mattico/high-gain-diff-probe/Sim/Comparator.asc

C1: cap; 0.1µ
C3: cap; 0.1µ
C4: cap; 10n
C5: cap; 0.1µ
D1: LED; NSCW100
R1: res; 7.15k
R2: res; 100k
R3: res; 7.15k
R4: res; 7.15k
R5: res; 7.15k
R6: res; 7.15k
R7: res; 10Meg
R8: res; 7.15k
R9: res; 100k
U1: LT1011
U2: LT1011
U3: LT1011
V1: voltage; 15
V2: voltage; 15
V3: voltage; PULSE(0 20 1m 10u 10u 0.1m); AC 1; Rser=50 Cpar=0.04p
Named nets: 0, +V, -V, IN, OUT, RC
.tran 0 50m 0
