mattico/high-gain-diff-probe/Sim/PowerInput_Boost_LT3580.asc

C1: cap; 10µ; V=25 Irms=0 Rser=0 Lser=0 mfg="Murata" pn="GRM21BZ71E106KE15" type="X7R"
C2: cap; 2.2n; Rser=10K
C3: cap; .1µ
C4: cap; 10µF
C5: cap; 1µ
C6: cap; 100p
C7: polcap; 47µ; V=25 Irms=70m Rser=0.526 Lser=18.5243n mfg="Würth Elektronik" pn="865090449007 WCAP-ASLU 8x6,5" type="Al electrolytic"
D1: schottky; 1N5818
L1: ind2; 27µ; Rser=.285
L2: ind2; 27µ; Rser=.285
R1: res; 450k
R2: res; 180k
Rload: res; 100
U1: LT3580
V1: voltage; 4.5; Rser=.5
Named nets: 0, IN, OUT
.tran 0 1m 0 10n startup
K1 L1 L2 1
