mattico/high-gain-diff-probe/Sim/PowerInput_LTM8049.asc

C3: cap; 10µ
C4: cap; 47µ; V=16 Irms=11.7 Rser=0.00333036 Lser=0 mfg="KEMET" pn="C1210C476K4PAC" type="X5R"
C5: cap; 22µ; V=25 Irms=0 Rser=0 Lser=0 mfg="Murata" pn="GRM32ER71E226KE15" type="X7R"
R1: res; 73.2k
R2: res; 165k
R3: res; 73.2k
R4: res; 178k
Rload1: res; 150
Rload2: res; 150
U1: LTM8049
V1: voltage; 4.5; Rser=0.4
Named nets: 0, IN, OUT1, OUT2
.tran 2m
