mattico/high-gain-diff-probe/Sim/PowerInput_Boost_LDO.asc

C1: cap; 1µ; V=25 Irms=0 Rser=0.001 Lser=0
C2: cap; 1µ; V=25 Irms=0 Rser=0.001 Lser=0
C3: cap; 1µ; V=35 Irms=0 Rser=0 Lser=0 mfg="Murata" pn="GCM21BR7YA105MA55" type="X7R"
C4: cap; 1µ; V=25 Irms=0 Rser=0 Lser=0 mfg="Murata" pn="GCM188R71E105MA64" type="X7R"
C5: cap; 10p; V=25 Irms=0 Rser=0 Lser=0 mfg="Murata" pn="GCM0335C1E100JA16" type="C0G"
C6: cap; 1µ; V=25 Irms=0 Rser=0.001 Lser=0 mfg="TDK" pn="C575OX7RIE106M" type="X7R"
C7: cap; 1µ; V=25 Irms=0 Rser=0.001 Lser=0 mfg="TDK" pn="C575OX7RIE106M" type="X7R"
C8: cap; 10µ; V=6.3 Irms=0 Rser=0 Lser=0 mfg="Murata" pn="GRM188R60J106ME84" type="X5R"
C9: polcap; 47µ; V=25 Irms=36m Rser=1.35945 Lser=2.49256n
C10: polcap; 47µ; V=25 Irms=36m Rser=1.35945 Lser=2.49256n
C11: cap; 1µ; V=25 Irms=0 Rser=0.00804838 Lser=269.844p mfg="Würth Elektronik" pn="885012207078 WCAP-CSGP 0805" type="X7R"
D1: schottky; MBRS130L
D2: diode; BAV199HM
D3: diode; BAV199HM
D4: diode; BAV199HM
D8: diode; BAV199HM
L1: ind; 22µ; Ipk=0.92 Rser=0.348
L2: ind; 22µ; Ipk=0.92 Rser=0.348
R1: res; 300k
R2: res; 1Meg
R3: res; 88k
R5: res; 1Meg
R6: res; 75k
R7: res; 83k
R8: res; 1Meg
RLoad1: res; 200
RLoad: res; 200
RProbe: res; 50
RTerm: res; 50k
U1: LT3088
U3: LT3463
U4: LT3015
V1: voltage; 4.5; Rser=0.6
Named nets: VOUT+, VOUT-, 0, VIN, VINT+, VINT-, FB1, FB2
.tran 0 10m 0 10n
;.ac dec 100 1 3.5Meg
