mattico/high-gain-diff-probe/Sim/DiffAmp_AD8428.asc

C1: cap; 10.4p
C2: cap; 10.4p
C3: cap; 1n
C4: cap; 1n
C11: cap; 10µ
D1: diode; BAV199HM
D2: diode; BAV199HM
D3: diode; BAV199HM
D4: diode; BAV199HM
D5: diode; BAV199HM
D6: diode; BAV199HM
R1: res; 33; tol=0.1
R2: res; 33; tol=0.1
R3: res; 50
R4: res; 225
R5: res; 33; tol=0.1
R6: res; 33; tol=0.1
R9: res; 10100
R10: res; 990k
R11: res; 10100
R13: res; 10.78k
R14: res; 11k
R15: res; 200; tol=0.1
R17: res; 225
R19: res; 1Meg
R20: res; 1Meg
R: res; 990k
U1: AD8428
U2: BUF634A
U3: OP1177
U4: AD8671
V1: voltage; 15; Rser=0
V2: voltage; 15; Rser=0
VDiff: voltage; SINE(0 .01 100k); AC 1
Named nets: -V, +V, 0, IN+, IN-, ATTEN+, ATTEN-, OUT, SE
.op
;.ac dec 100 10 10Meg
.tran 0 100u 0
;.noise V(OUT) VDiff dec 100 0.1 1Meg
Optional parallel InAmps to reduce noise. Increases output offset voltage.
Only effective when amplifier noise dominates input resistance noise.
AC Input: Reduces flatband noise by 1/2
HiZ Input: Increases noise
LoZ Input: Decreases noise by 20%
0 Ohm Input: Decreases noise by 25%
 
Sometimes they need to be deleted for the output simulation to work,
it'll output SNAN otherwise.
Offset Trim
Switchable 100kHz Low-Pass
100kHz: 8.2nF
Switchable Gain Resistor:
2000X - None
1000X - 6000 ohm
500X - 2000
100X - 316
50X - 154
10X - 30.2
