mattico/high-gain-diff-probe/Sim/DiffAmp_AD8428_Opt.asc

C1: cap; 8p
C4: cap; 14.7p
C5: cap; 14.7p
C9: cap; 1.5µ; V=100
C10: cap; 1.5µ; V=100
C11: cap; 10µ
C12: cap; 33n
C13: cap; 40p
C14: cap; 40p
D1: diode; BAV199HM
D2: diode; BAV199HM
D3: diode; BAV199HM
D4: diode; BAV199HM
D5: diode; BAV199HM
D6: diode; BAV199HM
R1: res; 950k
R2: res; 950k
R3: res; 50
R4: res; 50
R5: res; 33; tol=0.1
R5P: cap; .04p
R6: res; 33; tol=0.1
R6P: cap; .04p
R7: res; 1Meg
R8: res; 1Meg
R9: res; 562
R10: res; 562
R11: res; 475
R12: cap; .04p
R13: res; 9.7k
R14: res; 11k
R15: res; 50; tol=0.1
R16: res; 10k
R17: cap; .04p
R18: res; 20
R19: cap; .04p
R20: res; 475
R21: cap; .04p
R22: res; 10k
R23: res; 316
U1: AD8428
U4: LT1010
U5: ADA4004
V1: voltage; 15; Rser=0
V2: voltage; 15; Rser=0
VDiff: voltage; PULSE(0 .001 .1u 10n 10n .5u 2u); AC 1; Rser=25
Named nets: 0, -V, +V, IN+, IN-, ATTEN+, ATTEN-, OUT, SE
.op
;.ac dec 100 10 100Meg
;.tran 0 1u 0 1n
.noise V(OUT) VDiff dec 100 100 1G
LoZ Input: 50k to GND, 50 series
Protected to 40V
HiZ Input: 1Meg to GND, 950k series
AC Input: 2Hz -3dB with 1.5uF Input Capacitor
Optional parallel InAmps to reduce noise. Increases output offset voltage.
Only effective when amplifier noise dominates input resistance noise.
AC Input: Reduces flatband noise by 1/2
HiZ Input: Increases noise
LoZ Input: Decreases noise by 20%
0 Ohm Input: Decreases noise by 25%
 
Sometimes they need to be deleted for the output simulation to work,
it'll output SNAN otherwise.
Offset Trim
Switchable 100kHz Low-Pass
Switchable Gain Resistor:
2000X - None
1000X - 6000 ohm
500X - 2000
100X - 316
50X - 154
