mattico/high-gain-diff-probe/Sim/DiffAmp_Discrete.asc

J1: njf; LSK489A
J2: njf; LSK489A
J3: njf; LSK489A
J4: njf; LSK489A
R1: res; 1Meg
R2: res; {RS}
R3: res; {RS}
R4: res; 1Meg
R5: res; {RS}
R6: res; {RS}
U1: LT1995
V1: voltage; 15
V2: voltage; 15
V3: voltage; SINE(0 10u 10k); AC 1
Named nets: 0, VCC, VEE, OUT, IN+, IN-, IN+BUF, IN-BUF
;.tran 0 1m 0
.ac dec 100 10 50Meg
.param RS=750
