mattico/high-gain-diff-probe/Sim/PowerInput.asc

C1: cap; 10µ; V=25 Irms=0 Rser=0.001 Lser=0 mfg="TDK" pn="C575OX7RIE106M" type="X7R"
C2: cap; 10µ; V=25 Irms=0 Rser=0.001 Lser=0 mfg="TDK" pn="C575OX7RIE106M" type="X7R"
C3: cap; 0.1µ; V=50 Irms=0 Rser=0.0488383 Lser=600p mfg="Würth Elektronik" pn="885012205086 WCAP-CSGP 0402" type="X7R"
C4: polcap; 47µ; V=6.3 Irms=36m Rser=1.35945 Lser=2.49256n mfg="Würth Elektronik" pn="865230142003 WCAP-AS5H 5x5,5" type="Al electrolytic"
C5: polcap; 47µ; V=6.3 Irms=36m Rser=1.35945 Lser=2.49256n mfg="Würth Elektronik" pn="865230142003 WCAP-AS5H 5x5,5" type="Al electrolytic"
C6: cap; 10µ; V=25 Irms=0 Rser=0.001 Lser=0 mfg="TDK" pn="C575OX7RIE106M" type="X7R"
C7: cap; 10µ; V=25 Irms=0 Rser=0.001 Lser=0 mfg="TDK" pn="C575OX7RIE106M" type="X7R"
C9: polcap; 47µ; V=6.3 Irms=36m Rser=1.35945 Lser=2.49256n mfg="Würth Elektronik" pn="865230142003 WCAP-AS5H 5x5,5" type="Al electrolytic"
C10: polcap; 47µ; V=6.3 Irms=36m Rser=1.35945 Lser=2.49256n mfg="Würth Elektronik" pn="865230142003 WCAP-AS5H 5x5,5" type="Al electrolytic"
D1: diode; 1N4001
D2: diode; 1N4001
D3: zener; BZX84B16VL
D4: diode; BAV199HM
D5: zener; BZX84B16VL
D6: zener; BZX84B16VL
D7: zener; BZX84B16VL
D8: diode; BAV199HM
D9: diode; 1N4001
D10: diode; 1N4001
D11: diode; 1N4001
D12: diode; 1N4001
R1: res; 100
R2: res; 100
R3: res; 4.7k
R4: res; 4.7k
RLoad1: res; 200
RLoad: res; 50
RProbe: res; 50
RTerm: res; 50k
U1: TIP127
U2: TIP142
V1: battery; 9.6; Rser=1
V2: battery; 9.6; Rser=1
V3: battery; 9.6; Rser=1
V4: battery; 9.6; Rser=1
VFault: voltage; PULSE(0 40 1m 10u 10u 10m)
VNoise: voltage; 0
Named nets: 0, VOUT+, VOUT-
.MODEL 1N4001 D(
+IS=1.22478e-08 RS=0.0414786 N=1.83369 EG=0.6
+XTI=0.05 BV=50 IBV=5e-08 CJO=1e-11
+VJ=0.7 M=0.5 FC=0.5 TT=1e-09
+KF=0 AF=1)
.tran 0 50m 0 5u
.model LED D(Is=1e-19 N=1.6 Rs=2.5 Eg=2.1)
